ifilot/p2000t-cartridges/multicartridge-smd-32u4-front-dipswitch/case/multicolor/label-bottom.stl

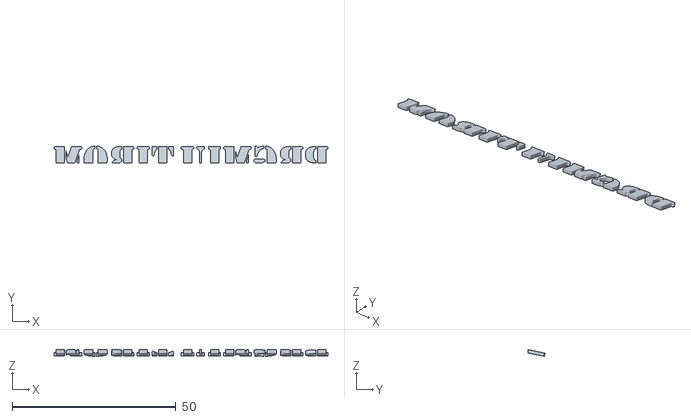
[picture p16: CAD file, 2026-09-05]
multicartridge-smd-32u4-front-dipswitch/case/multicolor/label-bottom.stl
83.7 x 5.21 x 2.04
