ifilot/p2000t-cartridges/multicartridge-w27c512/cases/multimaterial/p2000t_gamecartridge_w27c512_label_bottom.stl

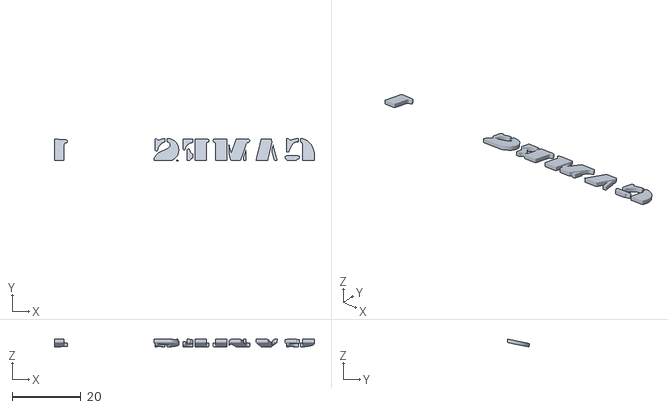
[picture p17: CAD file, 2025-01-25]
multicartridge-w27c512/cases/multimaterial/p2000t_gamecartridge_w27c512_label_bottom.stl
75.5 x 6.45 x 2.30
