ifilot/p2000t-cartridges/multicartridge-zif/case/p2000t_cartridge_zif_bottom.stl

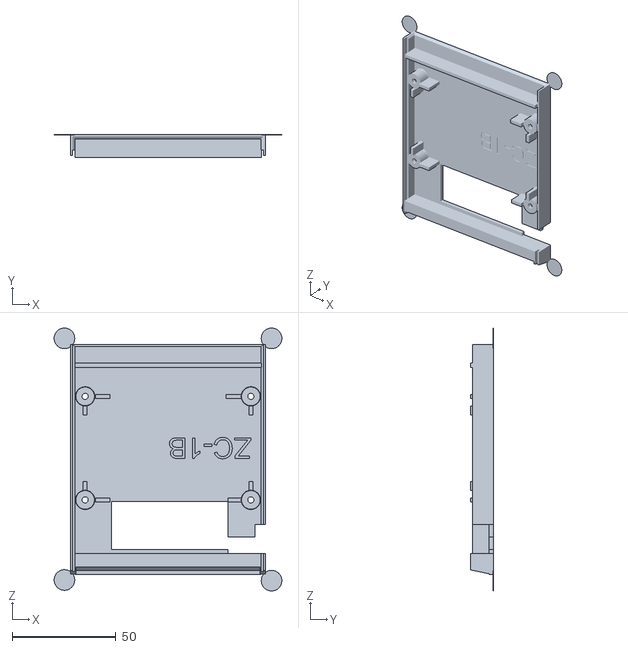
[picture p18: CAD file, 2023-09-24]
multicartridge-zif/case/p2000t_cartridge_zif_bottom.stl
110.0 x 11.0 x 127.0
