ifilot/p2000t-cartridges/multicartridge-sst39sf010/cases/p2000t_gamecartridge_ghost.stl

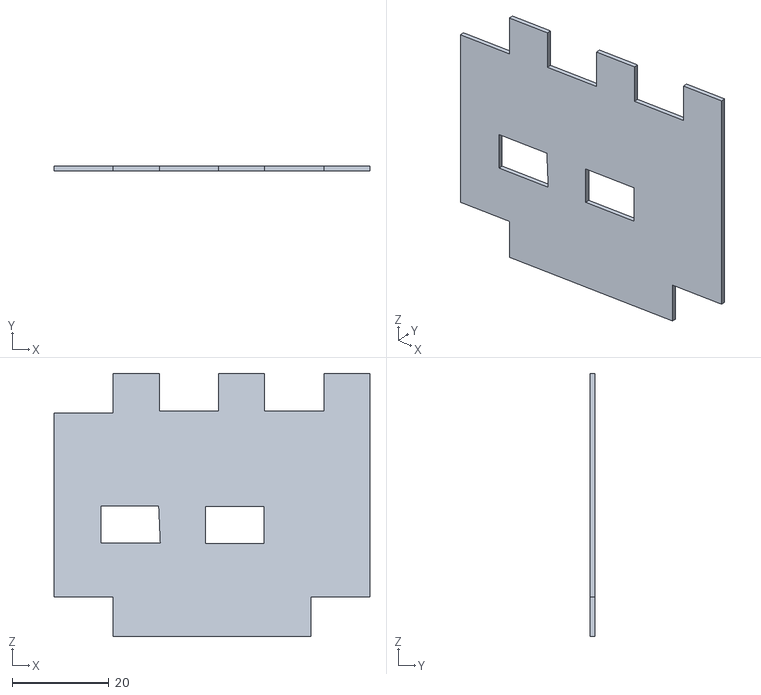
[picture p19: CAD file, 2025-01-02]
multicartridge-sst39sf010/cases/p2000t_gamecartridge_ghost.stl
65.3 x 1.00 x 54.4
