ifilot/p2000t-cartridges/multicartridge-sst39sf010/cases/p2000t_gamecartridge_label_bottom.stl

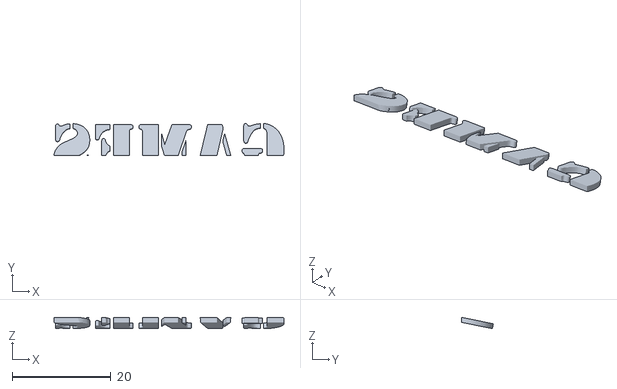
[picture p20: CAD file, 2025-01-02]
multicartridge-sst39sf010/cases/p2000t_gamecartridge_label_bottom.stl
46.7 x 6.45 x 2.30
