ifilot/p2000t-cartridges/multicartridge-tht-top-dipswitch/case/multimaterial/p2000t_multicartridge-label-cartridge-02.stl

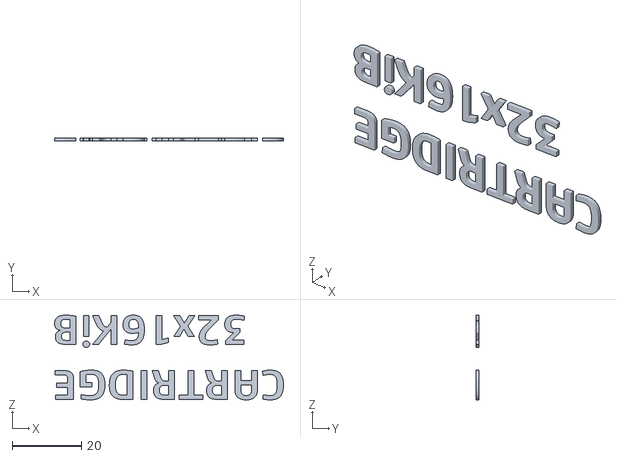
[picture p21: CAD file, 2024-06-15]
multicartridge-tht-top-dipswitch/case/multimaterial/p2000t_multicartridge-label-cartridge-02.stl
66.4 x 1.00 x 24.6
