ifilot/p2000t-cartridges/multicartridge-tht-top-dipswitch/case/multimaterial/p2000t_multicartridge-label-cartridge-01.stl

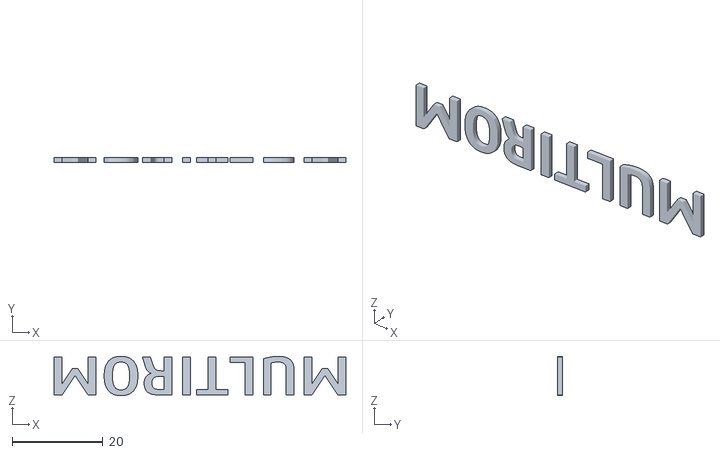
[picture p22: CAD file, 2024-06-15]
multicartridge-tht-top-dipswitch/case/multimaterial/p2000t_multicartridge-label-cartridge-01.stl
64.4 x 1.00 x 8.65
