ifilot/p2000t-cartridges/multicartridge-w27c512/cases/multimaterial/p2000t-multirom-w27c512-label-multirom.stl

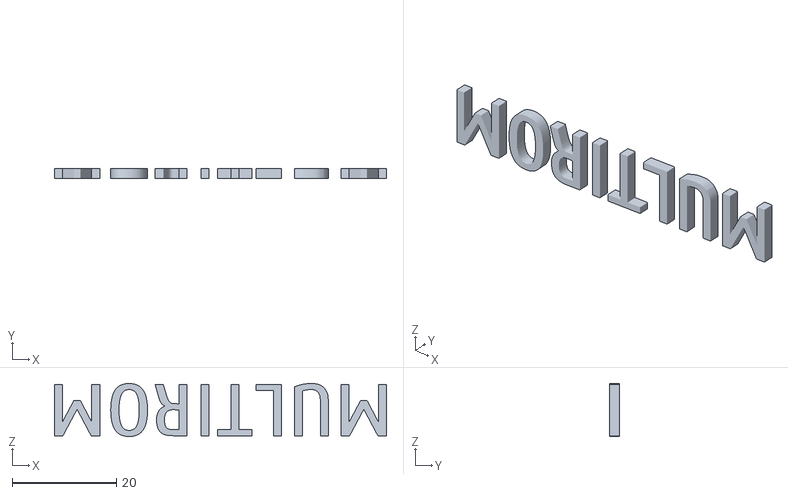
[picture p23: CAD file, 2024-06-15]
multicartridge-w27c512/cases/multimaterial/p2000t-multirom-w27c512-label-multirom.stl
63.7 x 2.00 x 10.2
