ifilot/p2000t-cartridges/multicartridge-w27c512/cases/multimaterial/p2000t-multirom-w27c512-label-0x40.stl

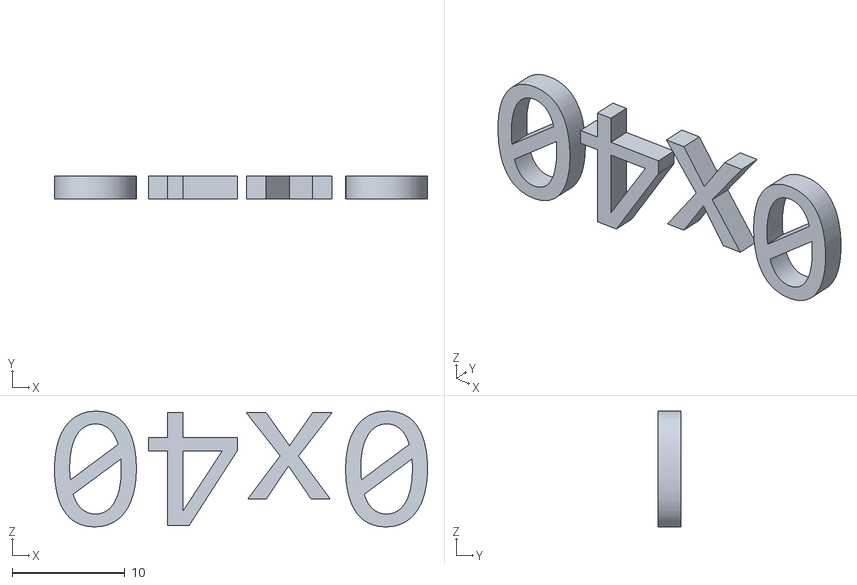
[picture p25: CAD file, 2024-06-15]
multicartridge-w27c512/cases/multimaterial/p2000t-multirom-w27c512-label-0x40.stl
33.1 x 2.00 x 10.3
